hajimen/p2ppcb_software/p2ppcb_component_reference/alice/schematic.png

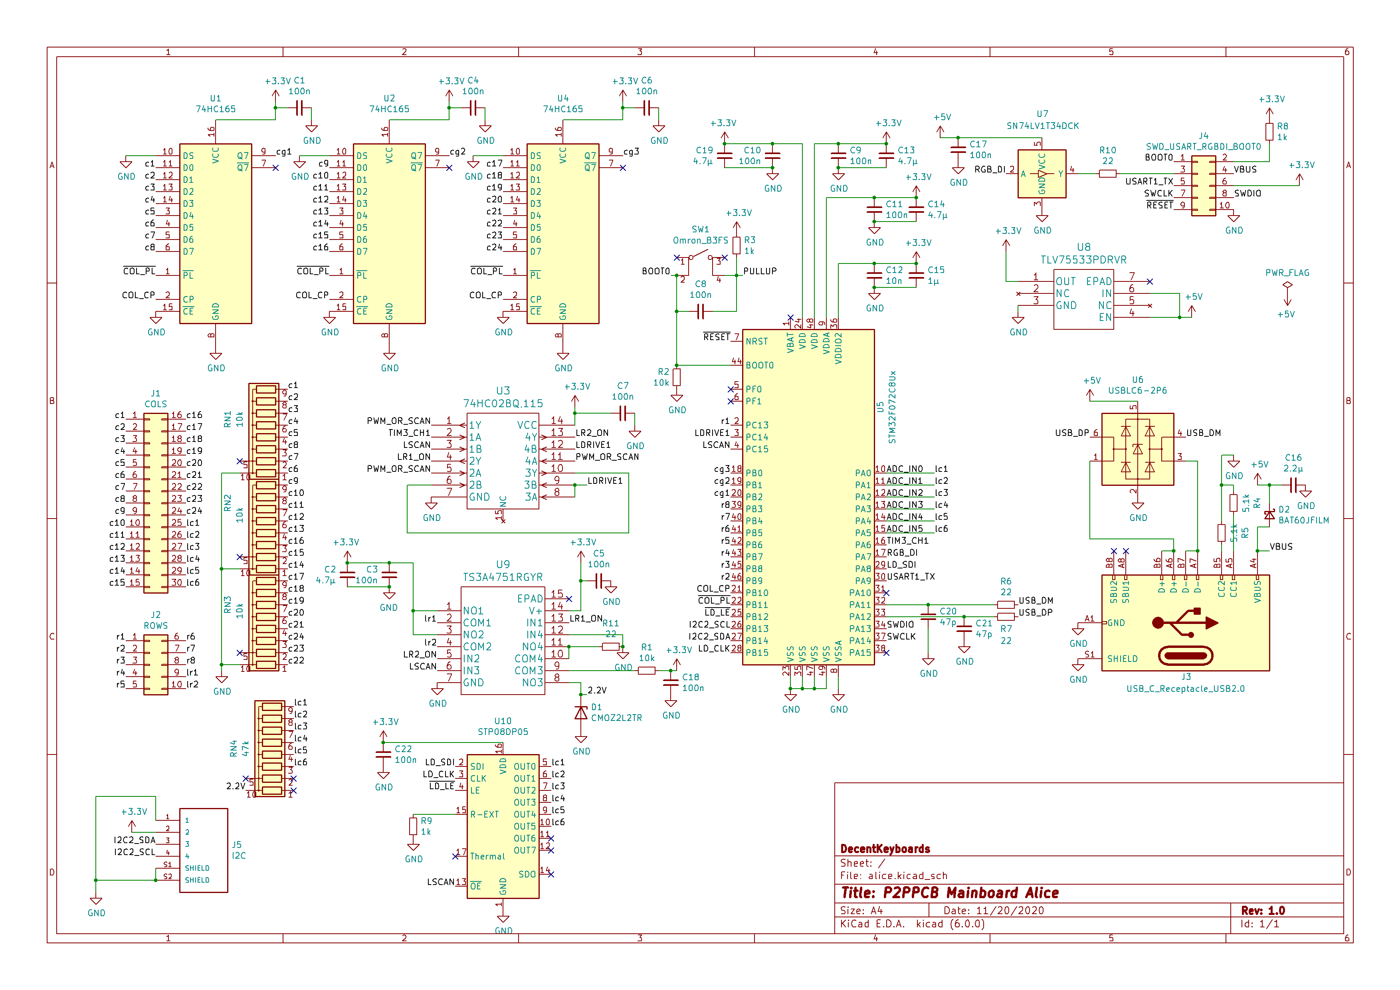
p2ppcb_component_reference/alice/schematic.png
