hajimen/p2ppcb_software/p2ppcb_component_reference/bob/schematic.png

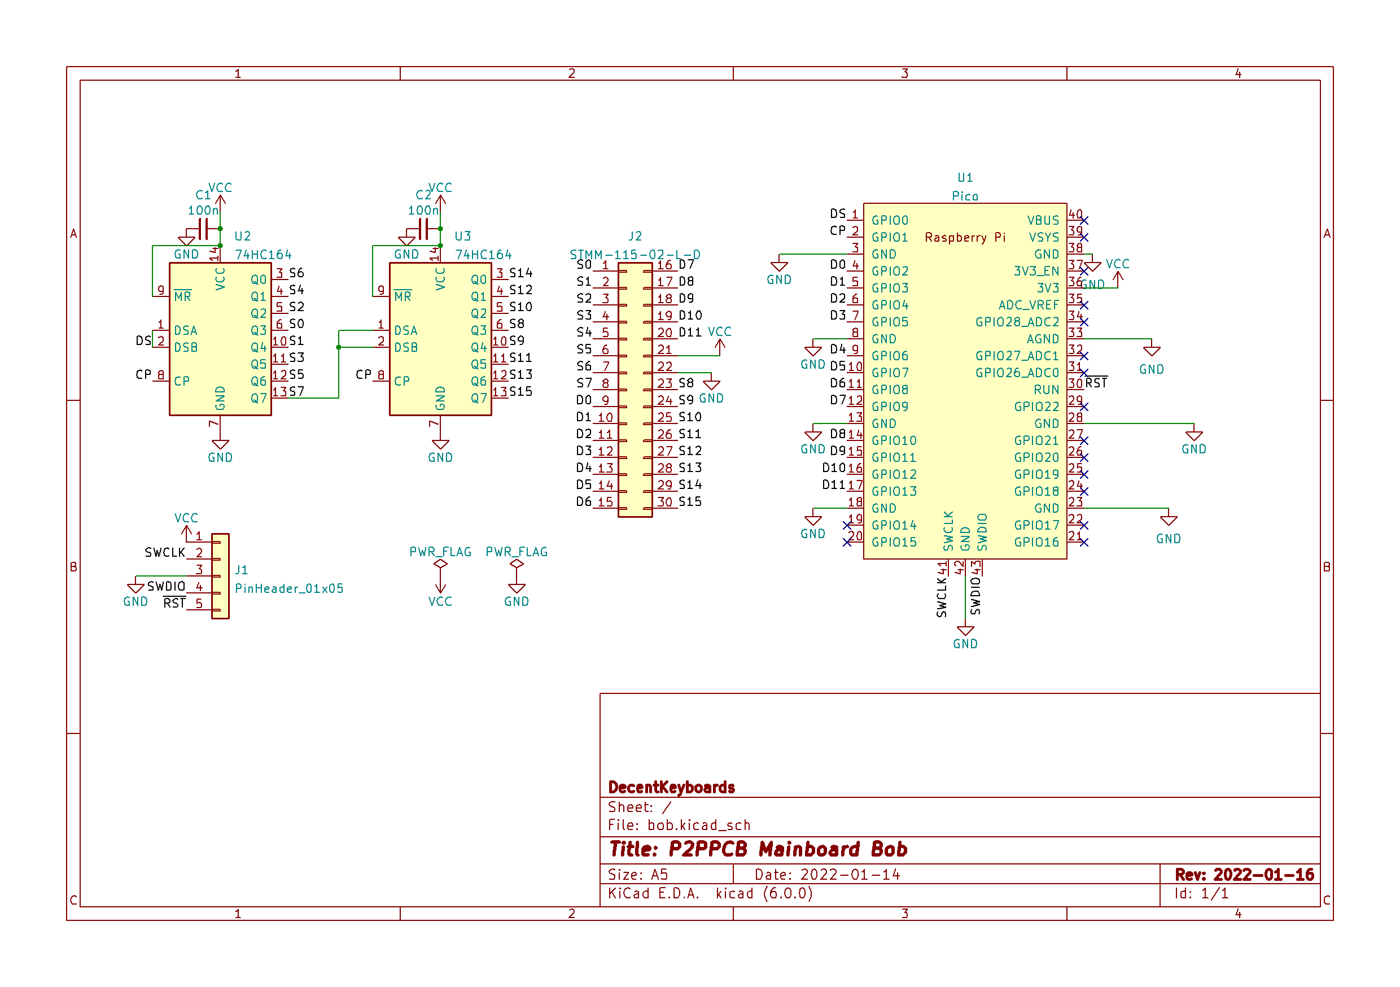
p2ppcb_component_reference/bob/schematic.png
