hajimen/p2ppcb_software/p2ppcb_component_reference/contact-to-socket/schematic-led.png

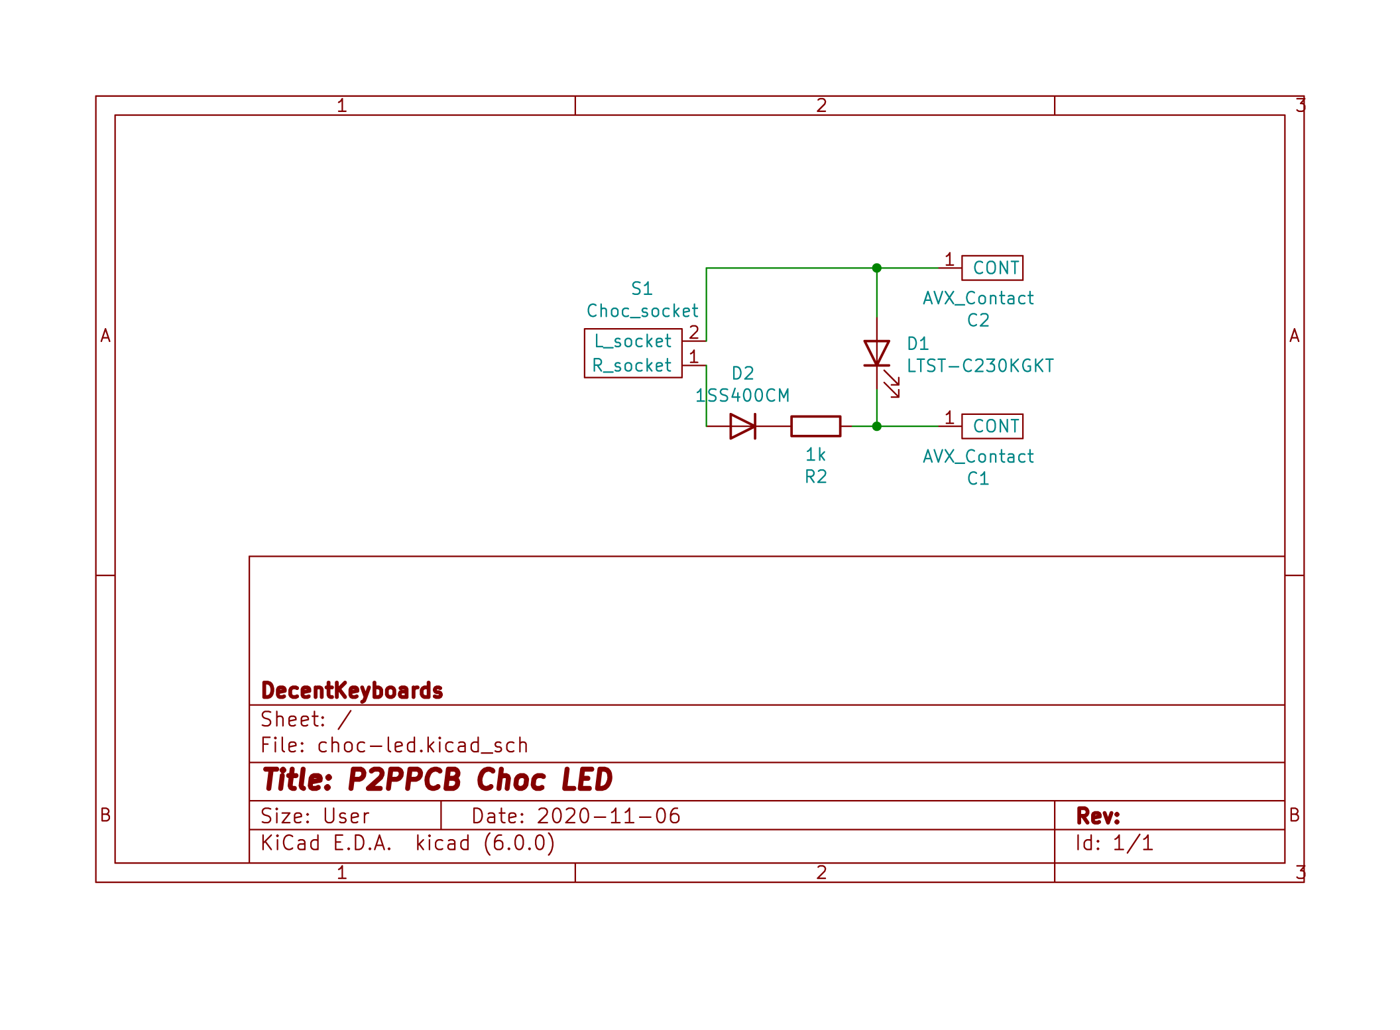
p2ppcb_component_reference/contact-to-socket/schematic-led.png
