hajimen/p2ppcb_software/p2ppcb_component_reference/qwiic-to-ffc/schematic-azoteq-cirque.png

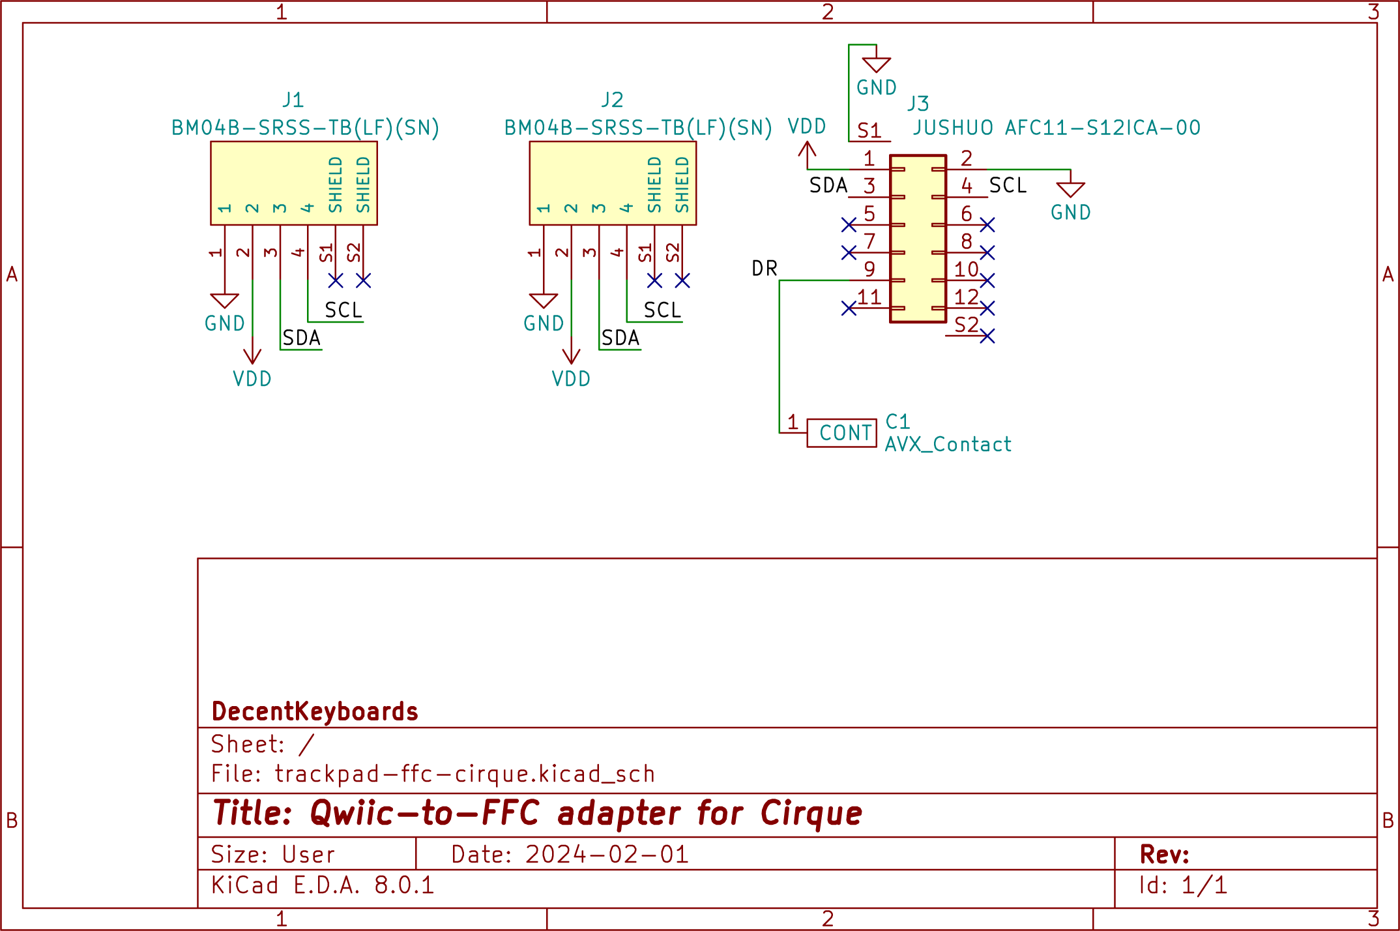
p2ppcb_component_reference/qwiic-to-ffc/schematic-azoteq-cirque.png
