hajimen/p2ppcb_software/p2ppcb_composer_f360/test_data/png/prepare_parts_sync_oracle.png

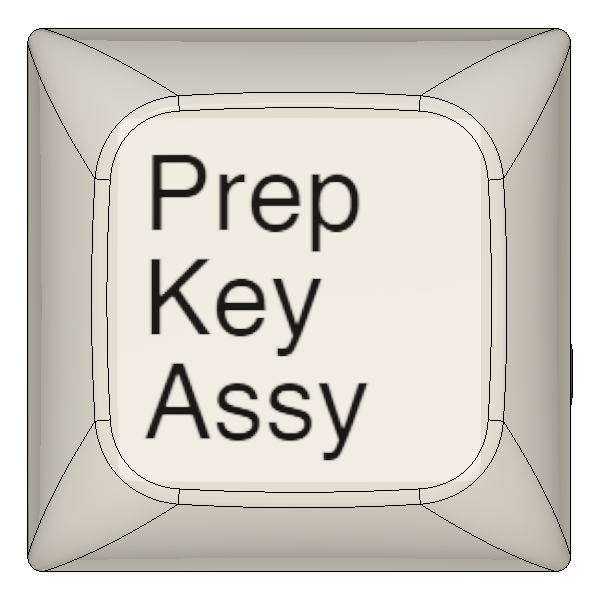
p2ppcb_composer_f360/test_data/png/prepare_parts_sync_oracle.png
