hajimen/p2ppcb_software/p2ppcb_parts_data_f360/png/PCB-MX-LED.png

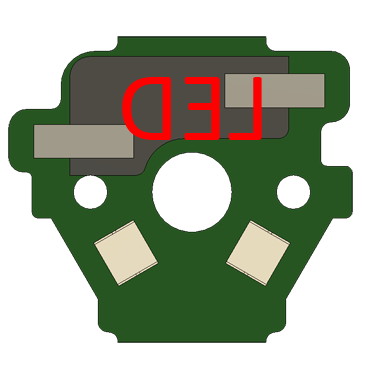
p2ppcb_parts_data_f360/png/PCB-MX-LED.png
