hajimen/p2ppcb_software/p2ppcb_ntcs/left/wiring_D.png

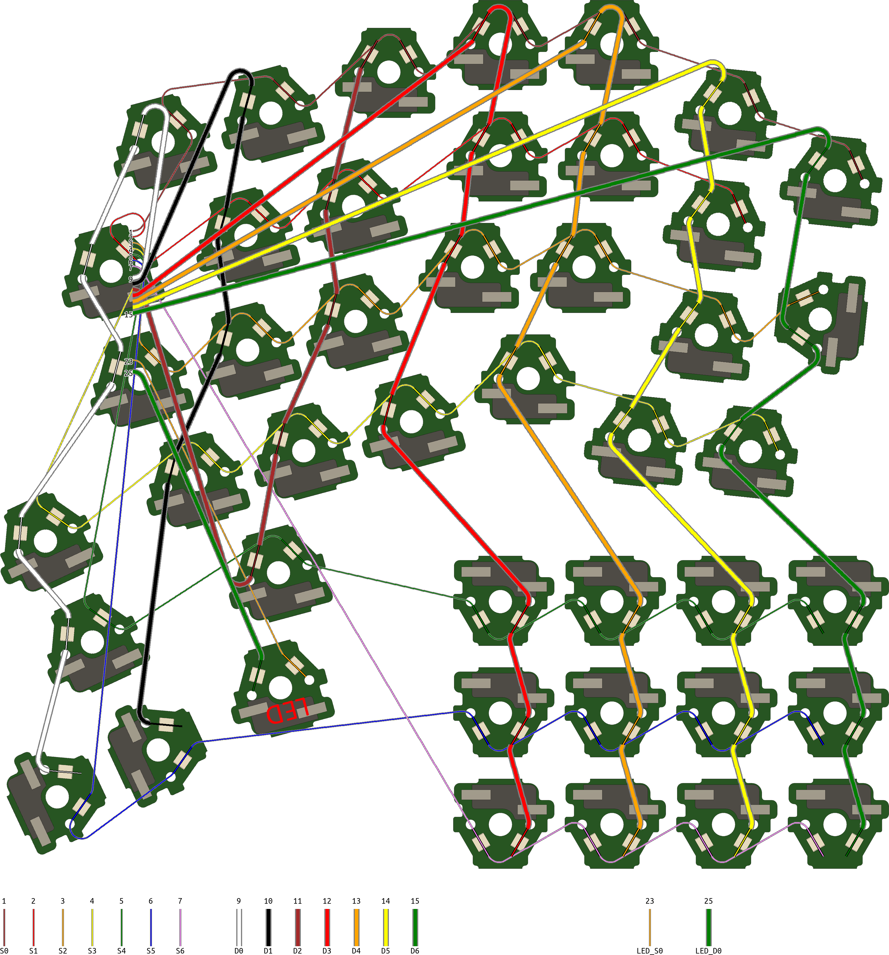
p2ppcb_ntcs/left/wiring_D.png
