hajimen/p2ppcb_software/p2ppcb_ntcs/left/wiring_S.png

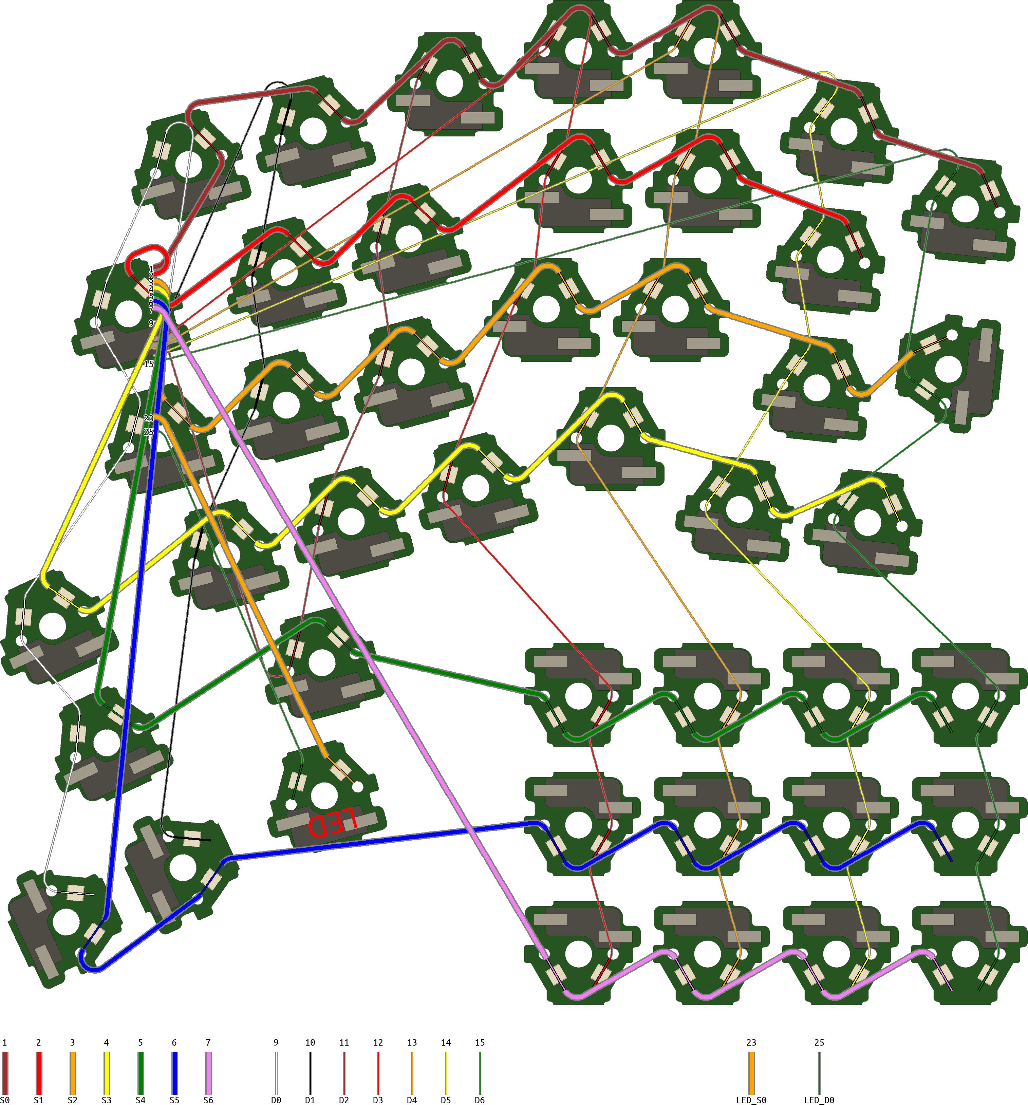
p2ppcb_ntcs/left/wiring_S.png
