hajimen/p2ppcb_software/p2ppcb_ntcs/right/wiring_D.png

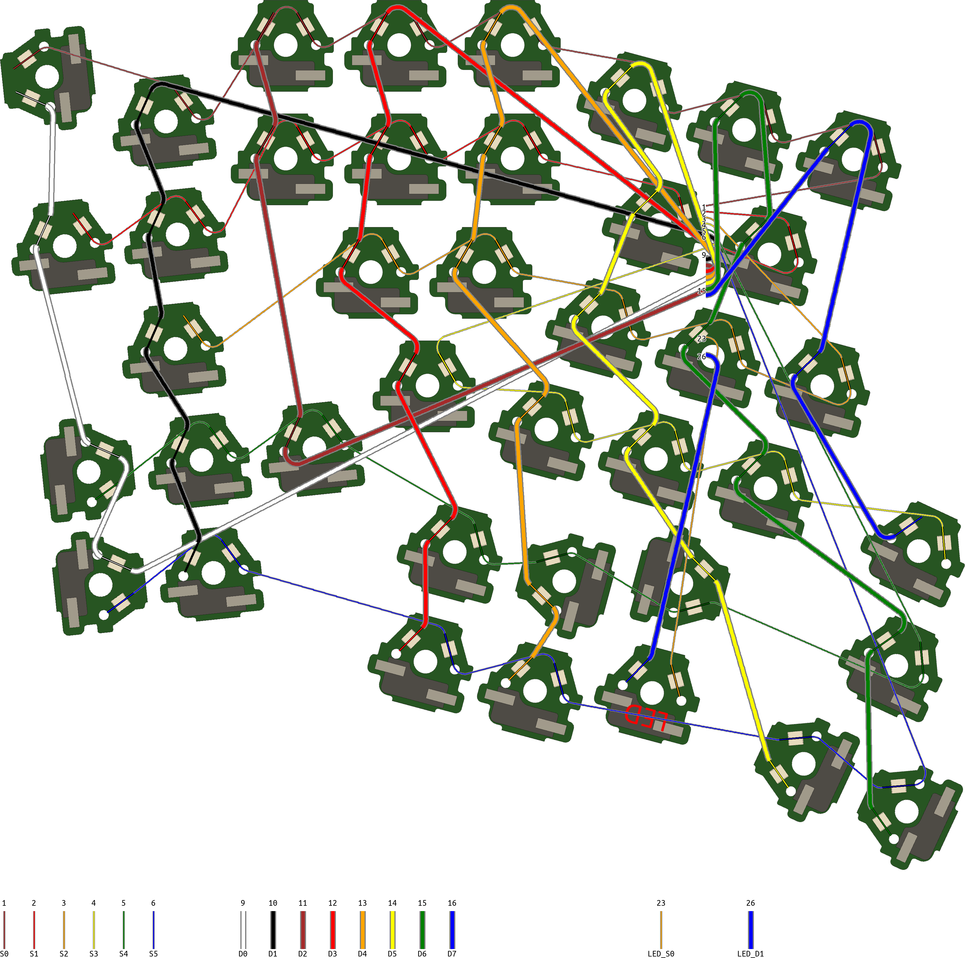
p2ppcb_ntcs/right/wiring_D.png
