hajimen/p2ppcb_software/p2ppcb_ntcs/right/wiring_S.png

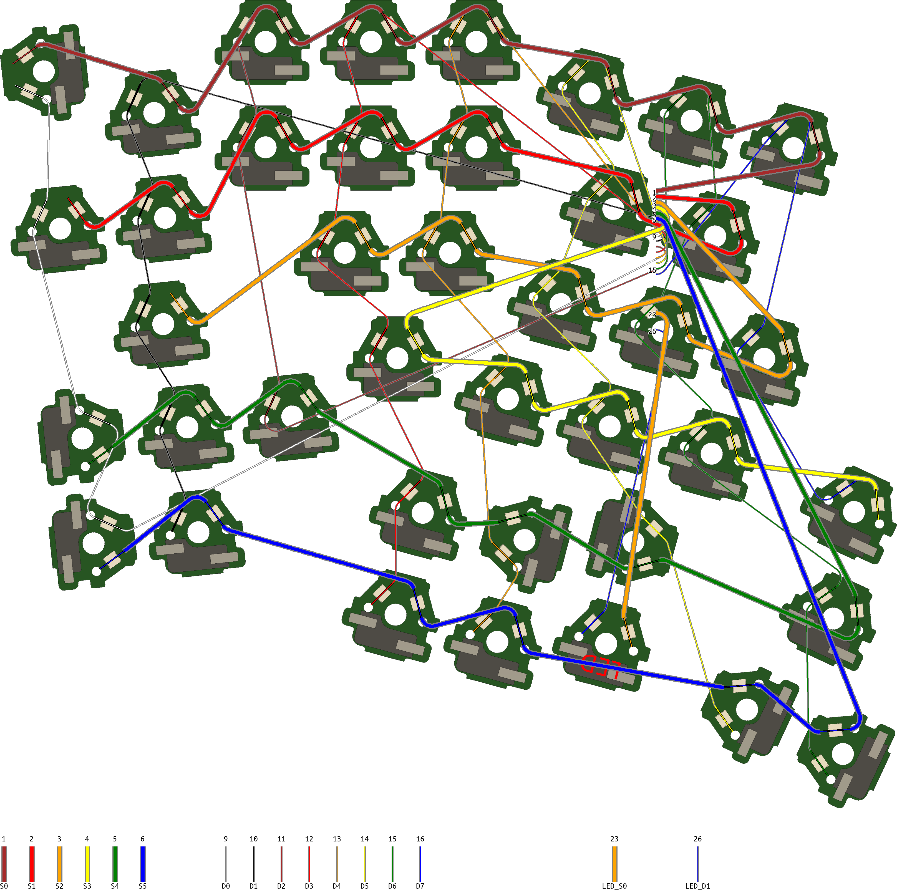
p2ppcb_ntcs/right/wiring_S.png
