hajimen/p2ppcb_software/p2ppcb_starter_kit_reference/bob/wiring_D.png

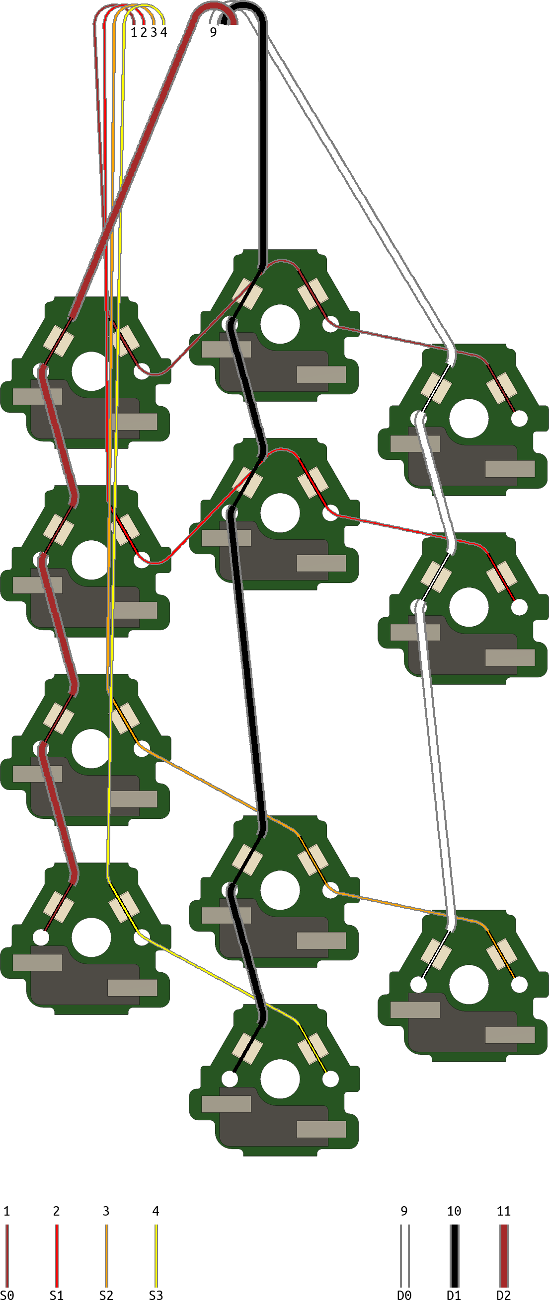
p2ppcb_starter_kit_reference/bob/wiring_D.png
