hajimen/p2ppcb_software/p2ppcb_starter_kit_reference/charlotte/wiring_S.png

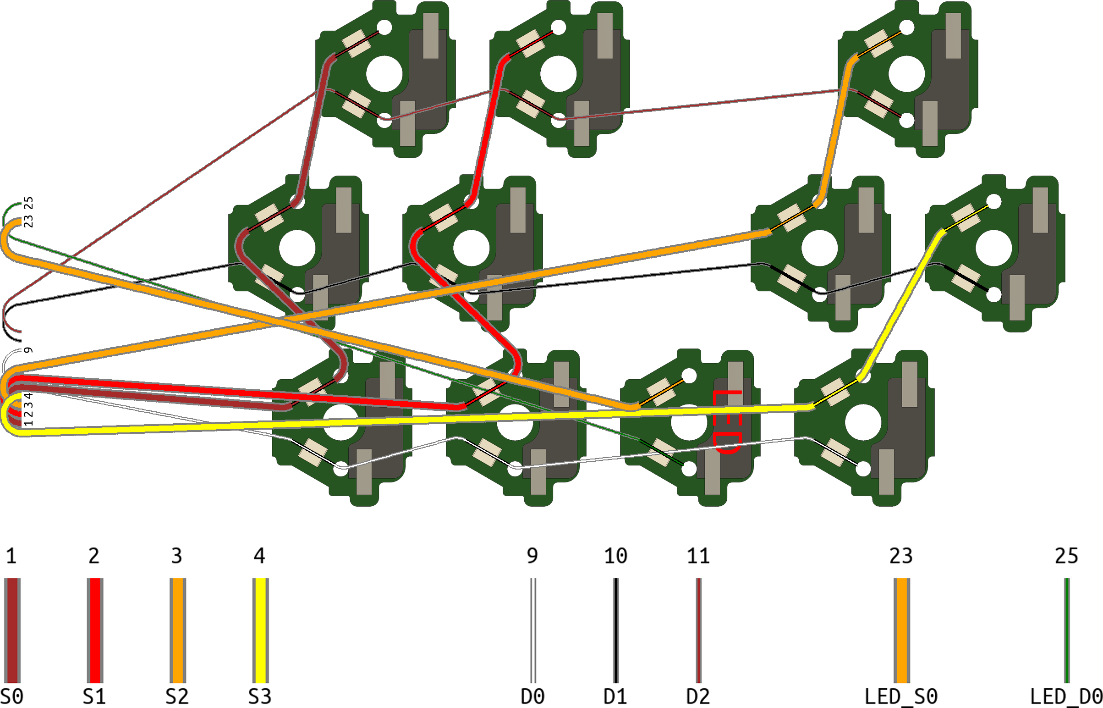
p2ppcb_starter_kit_reference/charlotte/wiring_S.png
