hajimen/p2ppcb_software/p2ppcb_composer_f360/test_data/png/choc_v1_cap_oracle.png

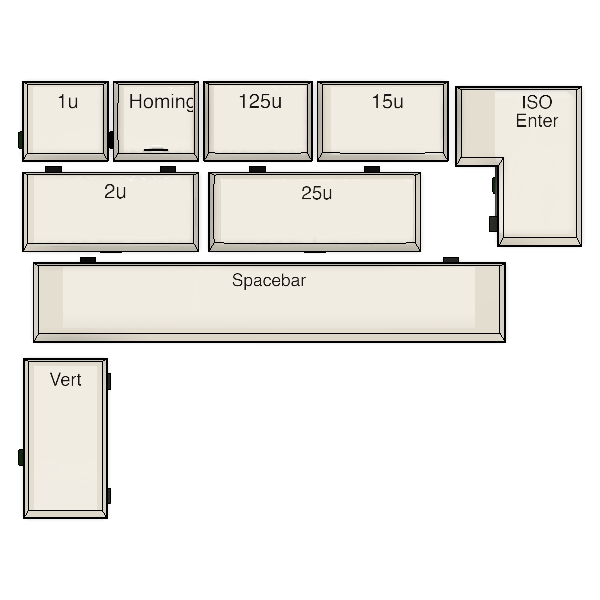
p2ppcb_composer_f360/test_data/png/choc_v1_cap_oracle.png
