hajimen/p2ppcb_software/p2ppcb_composer_f360/test_data/png/draw_wire_col.png

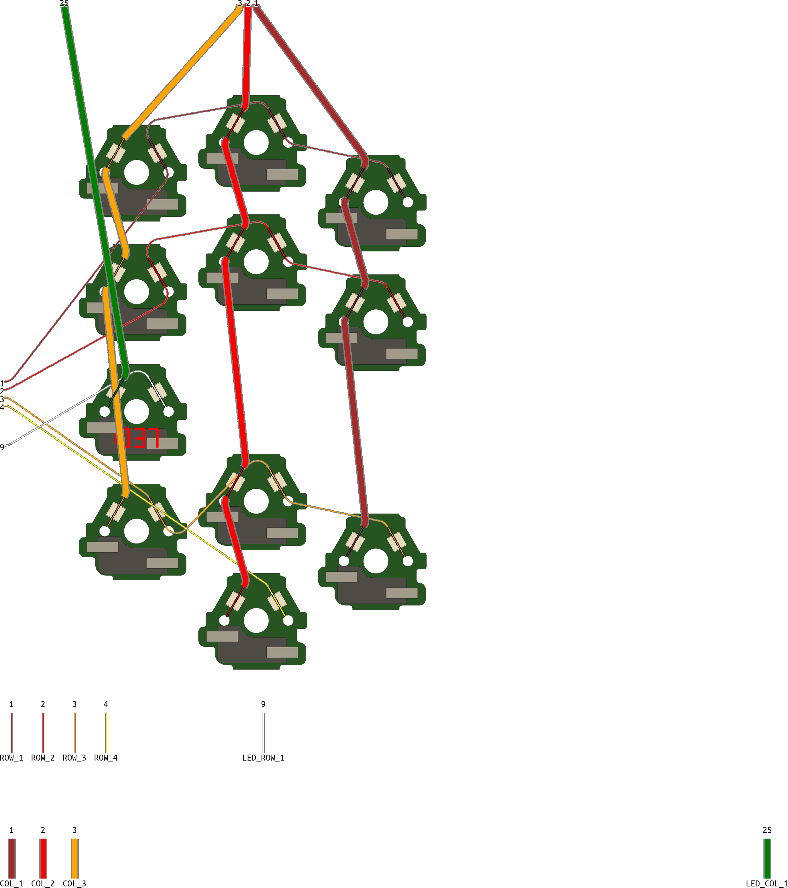
p2ppcb_composer_f360/test_data/png/draw_wire_col.png
