hajimen/p2ppcb_software/p2ppcb_parts_resolver/test_data/decal_image/1u.png

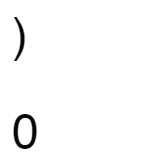
p2ppcb_parts_resolver/test_data/decal_image/1u.png
