hajimen/p2ppcb_software/p2ppcb_parts_resolver/test_data/decal_image/125u.png

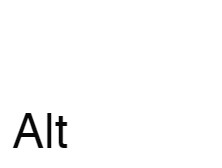
p2ppcb_parts_resolver/test_data/decal_image/125u.png
