hajimen/p2ppcb_software/p2ppcb_parts_resolver/test_data/kle/60percent.png

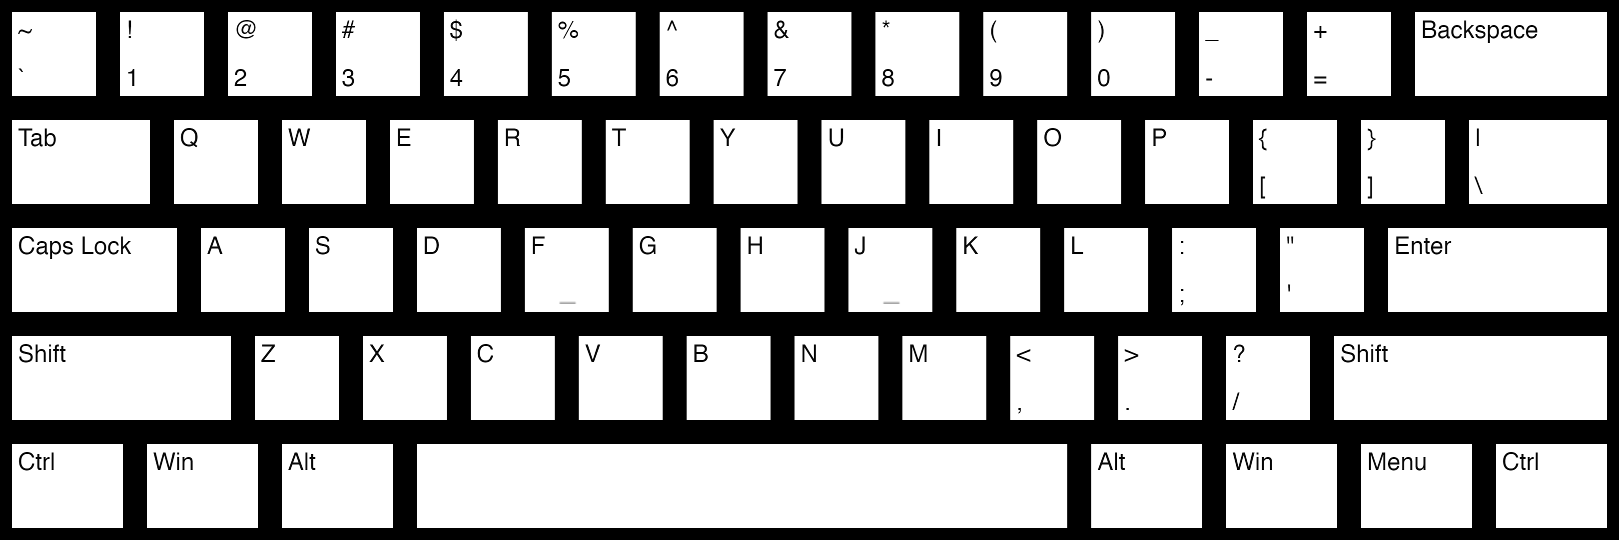
p2ppcb_parts_resolver/test_data/kle/60percent.png
