hajimen/p2ppcb_software/p2ppcb_parts_resolver/test_data/kle/ergodox.png

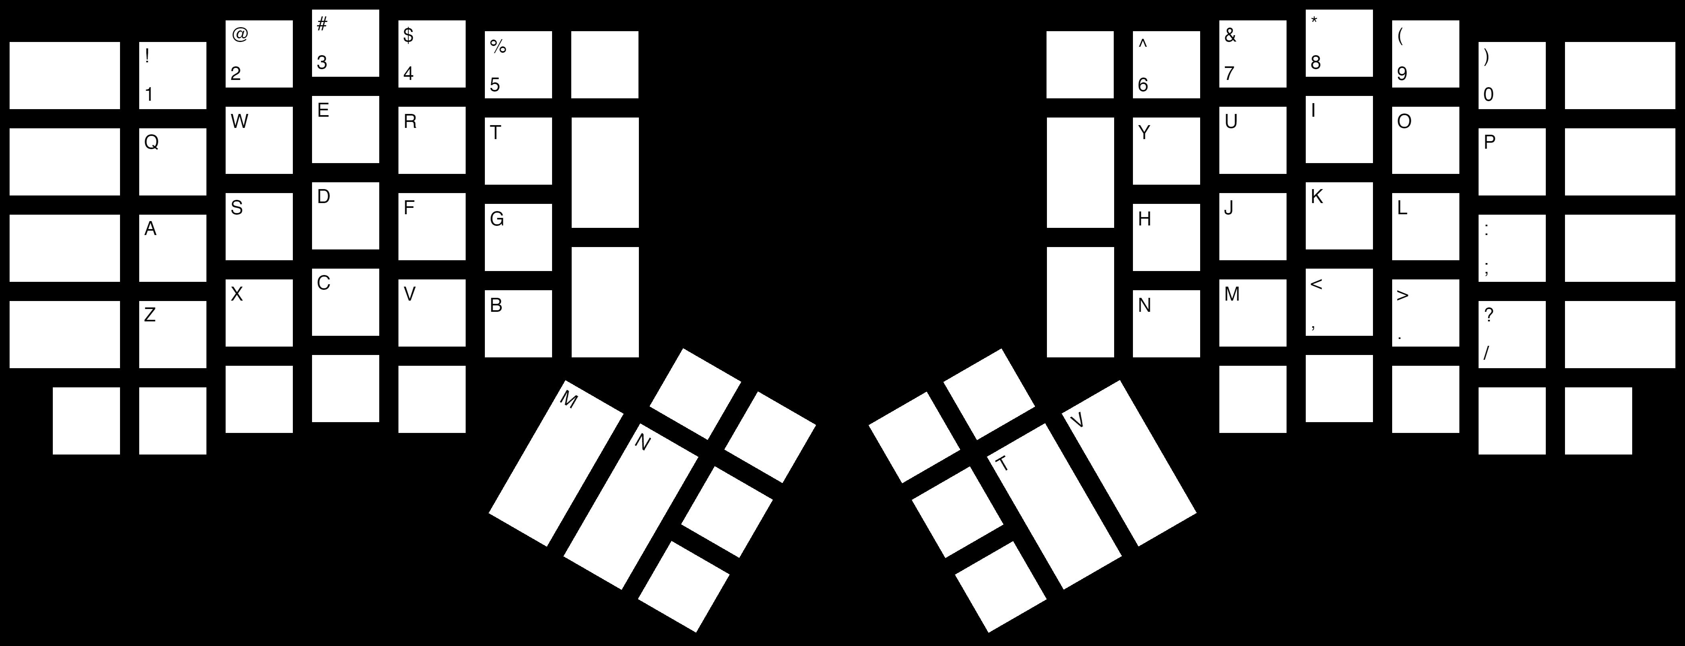
p2ppcb_parts_resolver/test_data/kle/ergodox.png
