hajimen/p2ppcb_software/p2ppcb_parts_resolver/test_data/kle/iso105.png

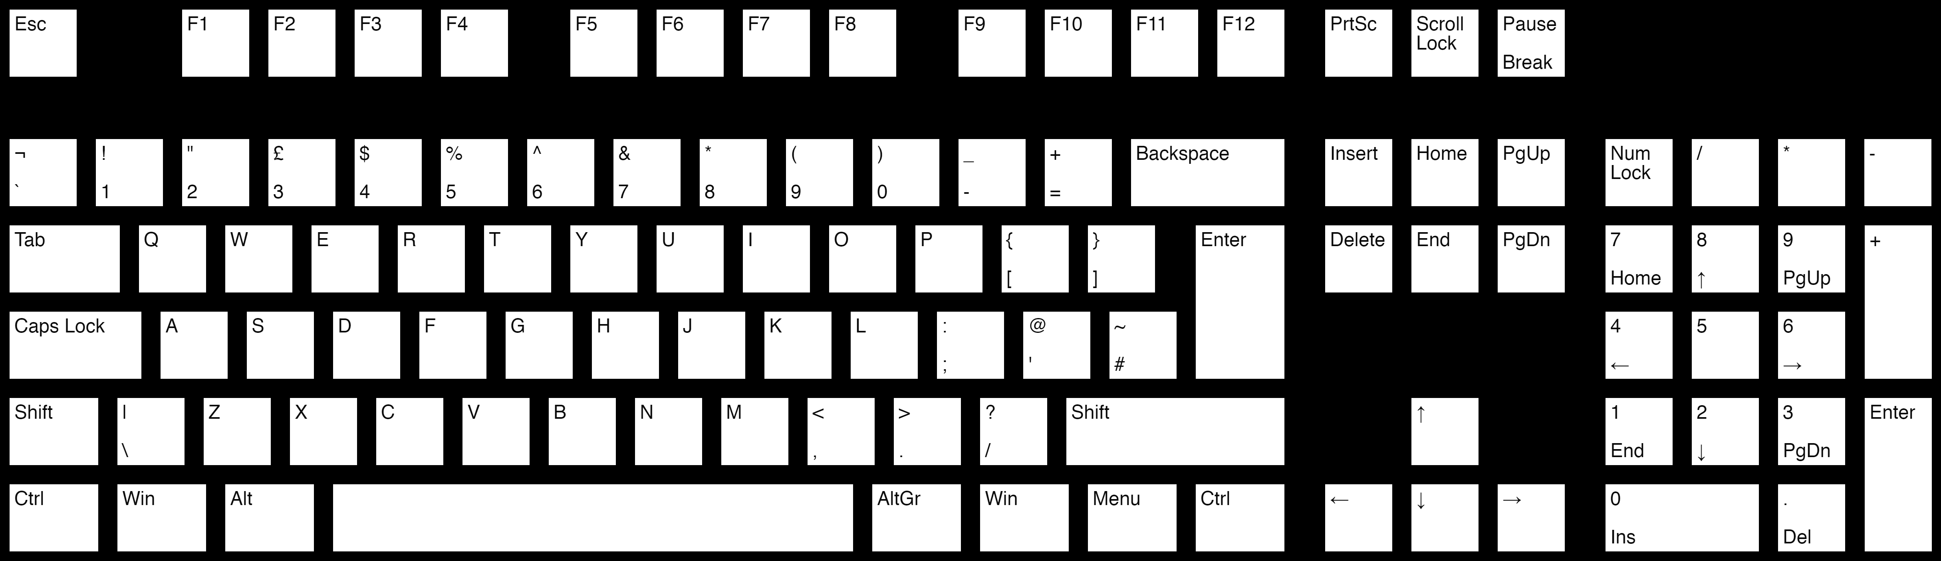
p2ppcb_parts_resolver/test_data/kle/iso105.png
