hajimen/p2ppcb_software/p2ppcb_parts_resolver/test_data/kle/stepped.png

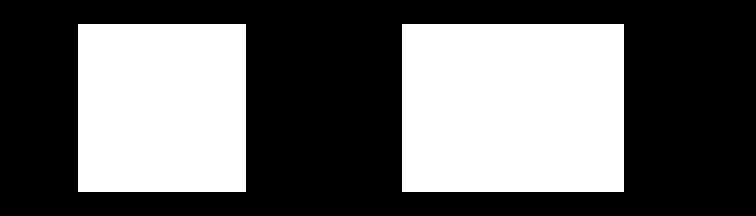
p2ppcb_parts_resolver/test_data/kle/stepped.png
